jbeuckm/PG328/atmega_midi_pg800/RotaryEncoder.h

#include "Arduino.h"

#define pinA 2
#define pinB 3


class RotaryEncoder {

private:
  int BUTTON_PIN; // will be pulled high and activated by connecting to 0V
  boolean buttonState;


  volatile byte aFlag; // let's us know when we're expecting a rising edge on pinA to signal that the encoder has arrived at a detent
  volatile byte bFlag; // let's us know when we're expecting a rising edge on pinB to signal that the encoder has arrived at a detent (opposite direction to when aFlag is set)
  volatile byte reading; //somewhere to store the direct values we read from our interrupt pins before checking to see if we have moved a whole detent
  
  void (*mRotateCallback)(int direction);
  void (*mButtonDownCallback)(void);
  void (*mButtonUpCallback)(void);
    
public:

  void PinA();
  void PinB();

  RotaryEncoder(int buttonPin);

  boolean checkButton();

  void setHandleRotate(void (*fptr)(int direction));
  void setHandleButtonDown(void (*fptr)(void));        
  void setHandleButtonUp(void (*fptr)(void));        
};
