jbeuckm/PG328/atmega_midi_pg800/PG800.cpp

#include "PG800.h"
#include <avr/pgmspace.h>

const char s0[] PROGMEM = "DCO1 Range";
const char s1[] PROGMEM = "DCO1 Wave";
const char s2[] PROGMEM = "DCO1 Tune";
const char s3[] PROGMEM = "DCO1 LFO";
const char s4[] PROGMEM = "DCO1 EG";
const char s5[] PROGMEM = "DCO2 Range";
const char s6[] PROGMEM = "DCO2 Wave";
const char s7[] PROGMEM = "XMOD";
const char s8[] PROGMEM = "DCO2 Tune";
const char s9[] PROGMEM = "DCO2 Fine Tune";
const char s10[] PROGMEM = "DCO2 LFO";
const char s11[] PROGMEM = "DCO2 EG";
const char s12[] PROGMEM = "";
const char s13[] PROGMEM = "";
const char s14[] PROGMEM = "";
const char s15[] PROGMEM = "DCO Dynamics";
const char s16[] PROGMEM = "DCO EG Mode";
const char s17[] PROGMEM = "DCO1 Level";
const char s18[] PROGMEM = "DCO2 Level";
const char s19[] PROGMEM = "Mix EG";
const char s20[] PROGMEM = "Mix Dynamics";
const char s21[] PROGMEM = "Mix EG Mode";
const char s22[] PROGMEM = "VCF HPF";
const char s23[] PROGMEM = "VCF Freq";
const char s24[] PROGMEM = "VCF Resonance";
const char s25[] PROGMEM = "VCF LFO";
const char s26[] PROGMEM = "VCF EG";
const char s27[] PROGMEM = "VCF Key";
const char s28[] PROGMEM = "VCF Dynamics";
const char s29[] PROGMEM = "VCF EG Mode";
const char s30[] PROGMEM = "VCA Level";
const char s31[] PROGMEM = "VCA Dynamics";
const char s32[] PROGMEM = "Chorus";
const char s33[] PROGMEM = "LFO Wave";
const char s34[] PROGMEM = "LFO Delay";
const char s35[] PROGMEM = "LFO Rate";
const char s36[] PROGMEM = "EG1 Attack";
const char s37[] PROGMEM = "EG1 Decay";
const char s38[] PROGMEM = "EG1 Sustain";
const char s39[] PROGMEM = "EG1 Release";
const char s40[] PROGMEM = "EG1 Key Follow";
const char s41[] PROGMEM = "EG2 Attack";
const char s42[] PROGMEM = "EG2 Decay";
const char s43[] PROGMEM = "EG2 Sustain";
const char s44[] PROGMEM = "EG2 Release";
const char s45[] PROGMEM = "EG2 Key Follow";
const char s46[] PROGMEM = "";
const char s47[] PROGMEM = "VCA EG Mode";

const char* const string_table[] PROGMEM = {
  s0, s1, s2, s3, s4, s5, s6, s7, s8, s9,
  s10, s11, s12, s13, s14, s15, s16, s17, s18, s19,
  s20, s21, s22, s23, s24, s25, s26, s27, s28, s29,
  s30, s31, s32, s33, s34, s35, s36, s37, s38, s39,
  s40, s41, s42, s43, s44, s45, s46, s47
};

volatile byte paramValues[48] = {
  63,63,63,63,63,63,63,63,
  63,63,63,63,63,63,63,63,
  63,63,63,63,63,63,63,63,
  63,63,63,63,63,63,63,63,
  63,63,63,63,63,63,63,63,
  63,63,63,63,63,63,63,63
};
volatile byte paramIndex;

#define PARAM_TYPES_COUNT 11
#define NUMERIC_PARAM 0
#define FOUR_VALUE_PARAM 1
#define WAVE_PARAM 2
#define RANGE_PARAM 3
#define XMOD_PARAM 4
#define EG_MODE_PARAM 5
#define TUNE_PARAM 6
#define FINE_PARAM 7
#define VCA_EG_MODE 8
#define LFO_WAVE 9
#define CHORUS 10

const byte paramTypes[48] PROGMEM = {
  RANGE_PARAM, WAVE_PARAM, TUNE_PARAM, NUMERIC_PARAM, NUMERIC_PARAM, RANGE_PARAM, WAVE_PARAM, XMOD_PARAM, 
  TUNE_PARAM, FINE_PARAM, NUMERIC_PARAM, NUMERIC_PARAM, NUMERIC_PARAM, NUMERIC_PARAM, NUMERIC_PARAM, FOUR_VALUE_PARAM, 
  EG_MODE_PARAM, NUMERIC_PARAM, NUMERIC_PARAM, NUMERIC_PARAM, FOUR_VALUE_PARAM, EG_MODE_PARAM, FOUR_VALUE_PARAM, NUMERIC_PARAM, 
  NUMERIC_PARAM, NUMERIC_PARAM, NUMERIC_PARAM, NUMERIC_PARAM, FOUR_VALUE_PARAM, EG_MODE_PARAM, NUMERIC_PARAM, FOUR_VALUE_PARAM, 
  CHORUS, LFO_WAVE, NUMERIC_PARAM, NUMERIC_PARAM, NUMERIC_PARAM, NUMERIC_PARAM, NUMERIC_PARAM, NUMERIC_PARAM, 
  FOUR_VALUE_PARAM, NUMERIC_PARAM, NUMERIC_PARAM, NUMERIC_PARAM, NUMERIC_PARAM, FOUR_VALUE_PARAM, NUMERIC_PARAM, VCA_EG_MODE
};

#include "ParamTypes.h"

// these functions have a version for each type of param
void (*incValueFunction[PARAM_TYPES_COUNT])(void);
void (*decValueFunction[PARAM_TYPES_COUNT])(void);
void (*setValueFunction[PARAM_TYPES_COUNT])(unsigned char value);
void (*drawValueFunction[PARAM_TYPES_COUNT])(Adafruit_SSD1306 *display);

PG800::PG800(int ready_pin, int clock_in_pin, int data_out_pin) : paramChanged(48), outBuffer(10) {
  
  incValueFunction[NUMERIC_PARAM] = inc_value_numeric;
  decValueFunction[NUMERIC_PARAM] = dec_value_numeric;
  setValueFunction[NUMERIC_PARAM] = set_value_numeric;
  drawValueFunction[NUMERIC_PARAM] = draw_value_numeric;

  incValueFunction[FOUR_VALUE_PARAM] = inc_value_4val;
  decValueFunction[FOUR_VALUE_PARAM] = dec_value_4val;
  setValueFunction[FOUR_VALUE_PARAM] = set_value_numeric;
  drawValueFunction[FOUR_VALUE_PARAM] = draw_value_4val;

  incValueFunction[WAVE_PARAM] = inc_value_4val;
  decValueFunction[WAVE_PARAM] = dec_value_4val;
  setValueFunction[WAVE_PARAM] = set_value_numeric;
  drawValueFunction[WAVE_PARAM] = draw_value_wave;

  incValueFunction[RANGE_PARAM] = inc_value_4val;
  decValueFunction[RANGE_PARAM] = dec_value_4val;
  setValueFunction[RANGE_PARAM] = set_value_numeric;
  drawValueFunction[RANGE_PARAM] = draw_value_range;

  incValueFunction[XMOD_PARAM] = inc_value_4val;
  decValueFunction[XMOD_PARAM] = dec_value_4val;
  setValueFunction[XMOD_PARAM] = set_value_numeric;
  drawValueFunction[XMOD_PARAM] = draw_value_xmod;

  incValueFunction[EG_MODE_PARAM] = inc_value_4val;
  decValueFunction[EG_MODE_PARAM] = dec_value_4val;
  setValueFunction[EG_MODE_PARAM] = set_value_numeric;
  drawValueFunction[EG_MODE_PARAM] = draw_value_eg_mode;

  incValueFunction[TUNE_PARAM] = inc_value_numeric;
  decValueFunction[TUNE_PARAM] = dec_value_numeric;
  setValueFunction[TUNE_PARAM] = set_value_numeric;
  drawValueFunction[TUNE_PARAM] = draw_value_tune;

  incValueFunction[FINE_PARAM] = inc_value_numeric;
  decValueFunction[FINE_PARAM] = dec_value_numeric;
  setValueFunction[FINE_PARAM] = set_value_numeric;
  drawValueFunction[FINE_PARAM] = draw_value_fine;

  incValueFunction[VCA_EG_MODE] = inc_value_4val;
  decValueFunction[VCA_EG_MODE] = dec_value_4val;
  setValueFunction[VCA_EG_MODE] = set_value_numeric;
  drawValueFunction[VCA_EG_MODE] = draw_value_vca_eg_mode;

  incValueFunction[LFO_WAVE] = inc_value_4val;
  decValueFunction[LFO_WAVE] = dec_value_4val;
  setValueFunction[LFO_WAVE] = set_value_numeric;
  drawValueFunction[LFO_WAVE] = draw_value_lfo_wave;

  incValueFunction[CHORUS] = inc_value_4val;
  decValueFunction[CHORUS] = dec_value_4val;
  setValueFunction[CHORUS] = set_value_numeric;
  drawValueFunction[CHORUS] = draw_value_chorus;
  

  READY_PIN = ready_pin;
  CLOCK_IN_PIN = clock_in_pin;
  DATA_OUT_PIN = data_out_pin;

  pinMode(READY_PIN, OUTPUT);
  digitalWrite(READY_PIN, LOW);

  pinMode(DATA_OUT_PIN, OUTPUT);
  digitalWrite(DATA_OUT_PIN, LOW);

  pinMode(CLOCK_IN_PIN, INPUT);

  paramIndex = 0;
}



int PG800::getParamIndex() {
  return paramIndex;
}


void PG800::queueByte(byte newByte) {
  sendQueue[sendQueueLength++] = newByte;
}

char buffer[20];

char *PG800::paramName() {
  strcpy_P(buffer, (char*)pgm_read_word(&(string_table[paramIndex])));
  return buffer;
}
byte PG800::paramValue() {
  return paramValues[paramIndex];
}

void PG800::nextParam() {
  if (paramIndex == 47) return;
  do {
    paramIndex++;
  } while (strcmp(paramName(), "") == 0);
}
void PG800::prevParam() {
  if (paramIndex == 0) return;
  do {
    paramIndex--;
  } while (strcmp(paramName(), "") == 0);
}
void PG800::setParam(byte param) {
  if (param < 0) return;
  if (param >= 48) return;
  paramIndex = param;
}

void PG800::incValue() {
  byte paramType = pgm_read_byte_near(paramTypes + paramIndex);
  incValueFunction[paramType]();
  paramChanged.setBit(paramIndex, true);
}
void PG800::decValue() {
  byte paramType = pgm_read_byte_near(paramTypes + paramIndex);
  decValueFunction[paramType]();
  paramChanged.setBit(paramIndex, true);
}
void PG800::setValue(byte value) {
  byte paramType = pgm_read_byte_near(paramTypes + paramIndex);
  setValueFunction[paramType](value);
  paramChanged.setBit(paramIndex, true);
}
void PG800::drawParamValue(Adafruit_SSD1306 *display) {
  byte paramType = pgm_read_byte_near(paramTypes + paramIndex);
  drawValueFunction[paramType](display);
}




void PG800::sendByte(byte data) {
  
  byte mask = B10000000;
  
  digitalWrite(READY_PIN, HIGH);
  
  for (int i=0; i<8; i++) {
    while (digitalRead(CLOCK_IN_PIN) == LOW) {
      delayMicroseconds(1);
    }
    if (data & mask) {
      digitalWrite(DATA_OUT_PIN, LOW);
    } else {
      digitalWrite(DATA_OUT_PIN, HIGH);
    }
    while (digitalRead(CLOCK_IN_PIN) == HIGH) {
      delayMicroseconds(1);
    }
    mask >>= 1;
  }
  
  digitalWrite(READY_PIN, LOW);
  delayMicroseconds(3);
}


void PG800::sync() {
  int updatedParamIndex = paramChanged.addressOfFirstSet();

  if (outBuffer.getLength() > 0) {
    while (outBuffer.getLength() > 0) {
      sendByte(outBuffer.shift());
    }
  }
  else if ((updatedParamIndex >= 0) && (updatedParamIndex < 48)) {
    outBuffer.push(PG800_PARAM_OFFSET + updatedParamIndex);
    outBuffer.push(paramValues[updatedParamIndex]);
    paramChanged.setBit(updatedParamIndex, false);
  }
}
